sparkfun/SparkFun_GNSS_Flex_Breakout/docs/assets/3d_model/poster.png

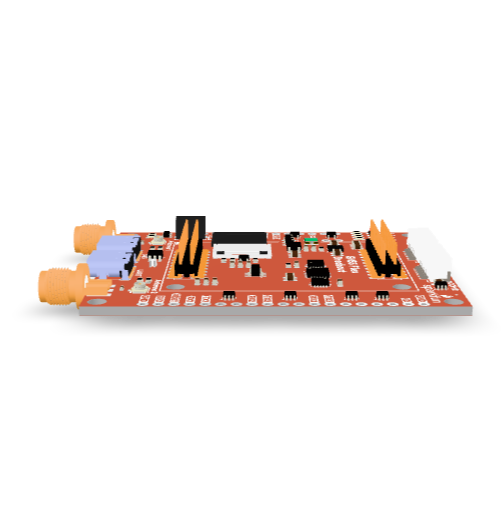
docs/assets/3d_model/poster.png
